keithiscool/XV11LidarDevPIC32/Software/lidarpic_FloatingPoint.X/SinLookupTable.c

//#include <xc.h>
//#include <stdbool.h>
//#include "SinLookupTable.h"
//
////Used unit circle to line up sine and cosine functions using just the first 90 degrees of the generated sine lookup table from excel:
////Lookup Table in Excel: \XV11LidarDevPIC32\Software\Archive\TestingTrigLookupTable
//
////Unit Circle (simple)
////https://upload.wikimedia.org/wikipedia/commons/thumb/4/4c/Unit_circle_angles_color.svg/2000px-Unit_circle_angles_color.svg.png
//
//
//
//unsigned short SinLookupTableArray[91] = { //Shorts are 16-bits large for PIC32.
//    0,
//    1144,
//    2287,
//    3430,
//    4572,
//    5712,
//    6850,
//    7987,
//    9121,
//    10252,
//    11380,
//    12505,
//    13626,
//    14742,
//    15855,
//    16962,
//    18064,
//    19161,
//    20252,
//    21336,
//    22415,
//    23486,
//    24550,
//    25607,
//    26656,
//    27697,
//    28729,
//    29753,
//    30767,
//    31772,
//    32768,
//    33754,
//    34729,
//    35693,
//    36647,
//    37590,
//    38521,
//    39441,
//    40348,
//    41243,
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
//};
//
//
//
//
//unsigned short GetMySinLookup16bit(short Degrees, bool *negativeNum) {
////    Degrees = Degrees % 360; // limit degrees between (-360<->360)
//
//    if (Degrees <= 90) {
//        *negativeNum = false;
//        return (SinLookupTableArray[Degrees]); // 0<Angle<90
//    }
//    if (Degrees <= 180) {
//        *negativeNum = false;
//        return (SinLookupTableArray[(180-Degrees)]); // 90<Angle<180
//    }
//
//    //these should not have to be used.
//    //[180,360] inclusive is behind the collection bucket, so the data is not useful
//    if (Degrees <= 270) {
//        *negativeNum = true;
//        return (SinLookupTableArray[(Degrees-180)]); // 180<Angle<270
//    }
//    if (Degrees <= 360) {
//        *negativeNum = true;
//        return (SinLookupTableArray[(360-Degrees)]); // 270<Angle<360
//    }
//    else {
////        printf("BAD_CARTESIAN_1\r\n");
//        return 0;
//    }
//}
//
//
//
////Use same lookup table for cosine to save space on pic32 microcontroller
//unsigned short GetMyCosLookup16bit(short Degrees, bool *negativeNum) {
////    Degrees = Degrees % 360; // limit degrees between (-360<->360)
//
//    if (Degrees <= 90) {
//        //take absolute value to line up math with a standard polar unit circle
//        *negativeNum = false;
//        return (SinLookupTableArray[abs(Degrees-90)]); // 0<Angle<90
//    }
//    if (Degrees <= 180) {
//        *negativeNum = true;
//        return (SinLookupTableArray[(Degrees-90)]); // 90<Angle<180
//    }
//
//    //these should not have to be used.
//    //[180,360] inclusive is behind the collection bucket, so the data is not useful
//    if (Degrees <= 270) {
//        *negativeNum = true;
//        return (SinLookupTableArray[(Degrees-180)]); // 180<Angle<270
//    }
//    if (Degrees <= 360) {
//        *negativeNum = false;
//        return (SinLookupTableArray[(360-Degrees)]); // 270<Angle<360
//    }
//    else {
////        printf("BAD_CARTESIAN_1\r\n");
//        return 0;
//    }
//}
//
//
////short GetMyCosLookup16bit(short Degrees, bool negativeNum){
//////    Degrees = Degrees % 360; // limit degrees between (-360<->360)
////
////    if (Degrees <= 90) return SinLookupTableArray[(90-Degrees)]; // 0<Angle<90
////    if (Degrees <= 180) return (-1*(SinLookupTableArray[(Degrees-90)])); // 90<Angle<180
//////    if (Degrees <= 270) return (-1*(SinLookupTableArray[(270-Degrees)])); // 180<Angle<270
//////    if (Degrees < 360) return (SinLookupTableArray[(Degrees-270)]); // 270<Angle<360
////    else{
//////        printf("BAD_CARTESIAN_2\r\n");
////        return 0;
////    }
////}
