keithiscool/XV11LidarDevPIC32/Software/lidarpic_FloatingPoint.X/interrupt_handler.c

#include <xc.h>
#include <sys/attribs.h>
#include <stdbool.h>
#include "interrupt_handler.h"


bool timeFlagOneHundMilSec = false;
bool timeFlagFiveSec = false;
bool timeFlagOneHundMilSecObjDet = false;
bool timeFlagOneHundMilSecObjectVelocity = false;
short timeHundMillisSinceObjectMoved = 0;

//100ms timer (PR = 31250, prescaler = 256)
void __ISR(_TIMER_3_VECTOR, IPL1AUTO) Timer3Handler(void)
{
    static unsigned int count = 0;
    count++;

    //5000ms has passed
    if( (timeFlagFiveSec == false) && (count > 50) ) //5000ms has passed
    {
        count = 0; //reset timer finished counter
        timeFlagFiveSec = true; //set global variable for use with rest of code outside this interrupt (timer done)
    }

    //100ms has passed
    if( (timeFlagOneHundMilSec == false) && (count > 1) ) //100ms has passed
    {
        timeFlagOneHundMilSec = true; //set global variable for use with rest of code outside this interrupt (timer done)
    }

    //100ms has passed (used in ObjectDetection.c while printing out the discovered object properties)
    if( (timeFlagOneHundMilSecObjDet == false) && (count > 1) ) //100ms has passed
    {
        timeFlagOneHundMilSecObjDet = true; //set global variable for use with rest of code outside this interrupt (timer done)
    }

    //100ms has passed (used in ObjectDetection.c while printing out the discovered object properties)
    if( (timeFlagOneHundMilSecObjectVelocity == false) && (count > 1) ) //100ms has passed
    {
        timeFlagOneHundMilSecObjectVelocity = true; //set global variable for use with rest of code outside this interrupt (timer done)
        timeHundMillisSinceObjectMoved++; //count number of "hundred milliseconds" have passed since the object was seen last
    }
    

    IFS0CLR = _IFS0_T3IF_MASK;
}
