keithiscool/XV11LidarDevPIC32/Software/lidarpic_FloatingPoint.X/interrupt_handler.h

/* File:   interrupt_handler.h
 * Author: Keith
 * Created on May 13, 2016, 12:02 AM*/

#ifndef INTERRUPT_HANDLER_H
#define	INTERRUPT_HANDLER_H

extern bool timeFlagFiveSec;
extern bool timeFlagOneHundMilSec;
extern bool timeFlagOneHundMilSecObjDet;
extern bool timeFlagOneHundMilSecObjectVelocity;
extern short timeHundMillisSinceObjectMoved;

#endif	/* INTERRUPT_HANDLER_H */
