keithiscool/XV11LidarDevPIC32/Software/Wii_Camera_5_17_2016_8/interrupt_handler.h

/* 
 * File:   interrupt_handler.h
 * Author: Dana
 *
 * Created on May 11, 2016, 10:13 PM
 */

#ifndef INTERRUPT_HANDLER_H
#define	INTERRUPT_HANDLER_H

#ifdef	__cplusplus
extern "C" {
#endif




#ifdef	__cplusplus
}
#endif

#endif	/* INTERRUPT_HANDLER_H */
