keithiscool/XV11LidarDevPIC32/Software/lidarpic_FloatingPoint.X/initialize.h

/* File:   initialize.h
 * Author: Igor & Keith
 * Created on July 3, 2015, 1:14 PM
 */

#ifndef INITIALIZE_H
#define	INITIALIZE_H

#include "defs.h"


// prototype for input ring buffer
struct ringBuff
{
    unsigned char buf[RING_BUF_SIZE];
    int head;
    int tail;
    int count;
};

extern struct ringBuff buffer_five;
extern int returned_data[10];

void initialize(void);
void IOpins(void);
void timers(void);
void PWM(void);
void UART(void);
void DMA(void);

extern void beginLIDARdecoder(unsigned int * _output_data, struct ringBuff* _input_data);
extern void delay(void);

///////////////////////////////////////////////////////////////////////////////////////////////////////////////////
//DMA Variables and Definitions Below:


////dma arrays for transmit (make a separate array for each DMA channel)
//extern unsigned char dma_one_array[SIZE_OF_DMA_ARRAY];

//// filled with class pointers to the send class
//extern struct *queue_One_Pointer; // use only 1 DMA channel (increase array size to use more DMA channels)

//// object declaration for send struct
//extern struct DMA_Buffer_One;

//dma settings struct
extern struct dmaSettings arrayOFdmaSetting[1];

// declarations for dma arrays for transmit
extern unsigned char dma_one_array[SIZE_OF_DMA_ARRAY];

//// declaration for dma settings
//extern struct dmaSettings dmaOneSettings; // use only 1 DMA channel (increase array size to use more DMA channels)

//Use the ring buffer for outputting to the DMA (DMA channel 1)
extern struct ringBuff buffer_one;

extern void queue_begin(struct dmaSettings *_settings, int module_number);

#endif	/* INITIALIZE_H */
